ginge/footpedal/STL/pedal assm - switch assm-1 switchbody-1.STL

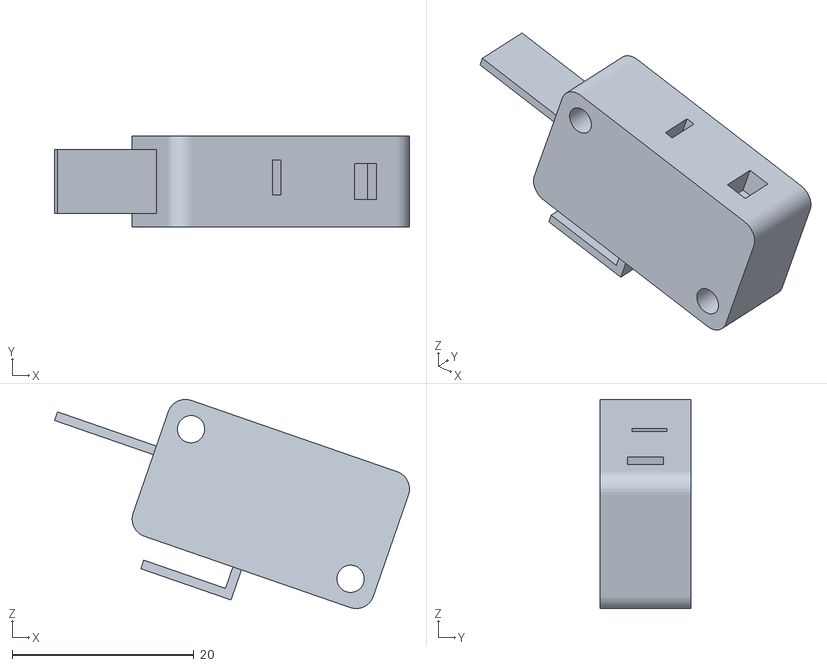
[picture p18: CAD file, 2014-02-17]
STL/pedal assm - switch assm-1 switchbody-1.STL
39.0 x 9.95 x 23.0
