ginge/footpedal/Foot Pedal Sld/pot cog.SLDPRT

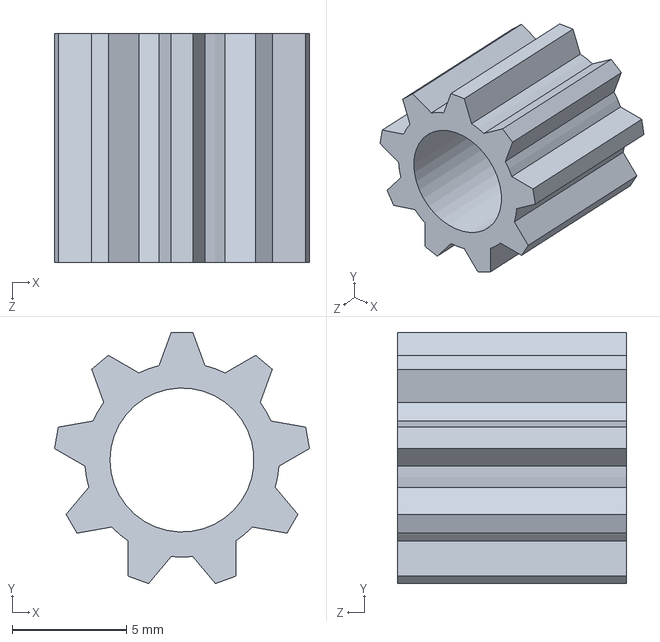
[picture p19: CAD file, 2014-02-17]
Foot Pedal Sld/pot cog.SLDPRT
11.2 x 11.0 x 10.0 mm
