ginge/footpedal/Foot Pedal Sld/pedal.SLDPRT

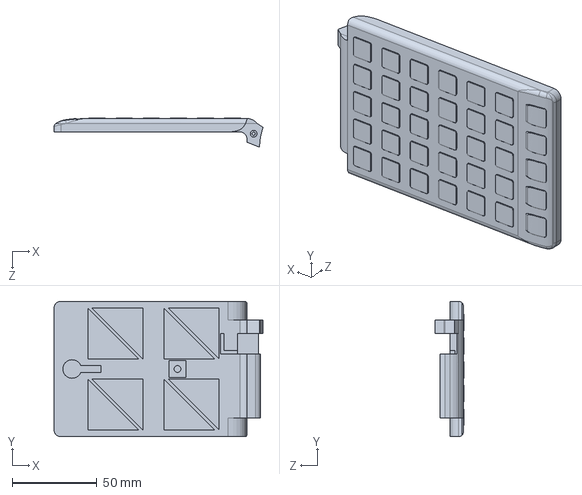
[picture p20: CAD file, 2014-02-17]
Foot Pedal Sld/pedal.SLDPRT
123.5 x 80.0 x 17.4 mm
