ginge/footpedal/STL/pedal assm - pot slide-1.STL

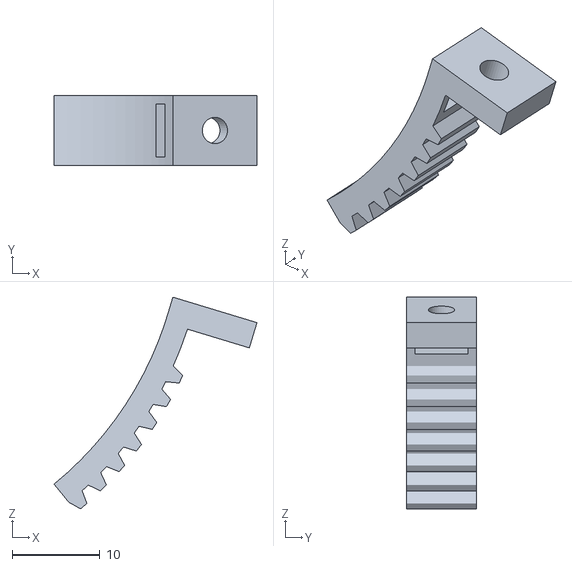
[picture p21: CAD file, 2014-02-17]
STL/pedal assm - pot slide-1.STL
23.1 x 8.00 x 24.1
