ginge/footpedal/Foot Pedal Sld/back panel.SLDPRT

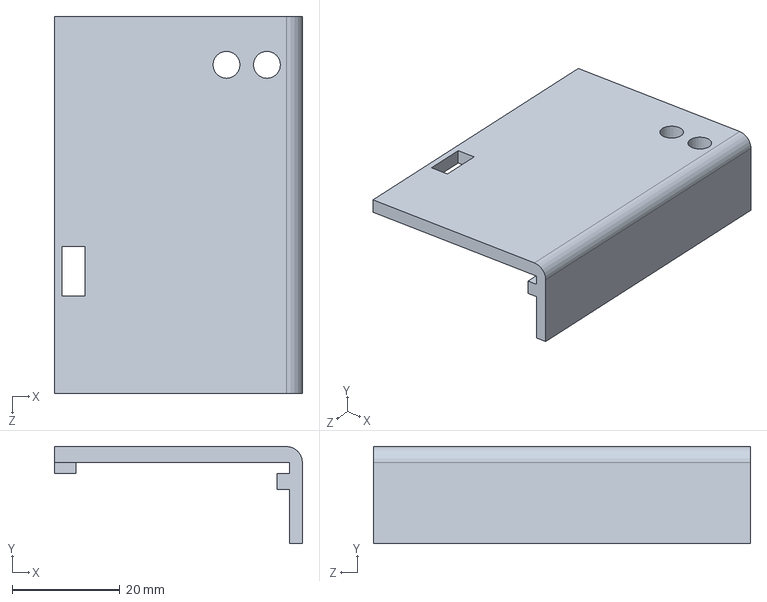
[picture p22: CAD file, 2014-02-17]
Foot Pedal Sld/back panel.SLDPRT
46.0 x 18.0 x 70.0 mm
