ginge/footpedal/STL/pedal assm - peg spring-1.STL

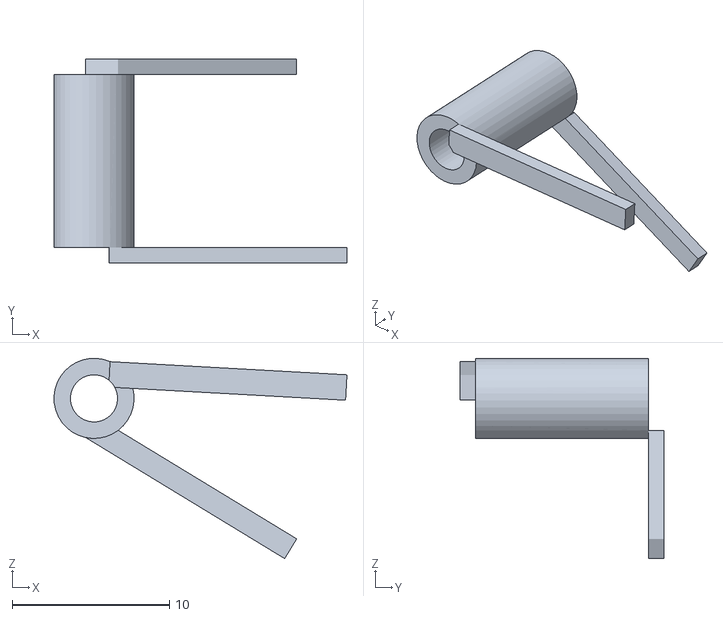
[picture p23: CAD file, 2014-02-17]
STL/pedal assm - peg spring-1.STL
18.6 x 13.0 x 12.7
