ginge/footpedal/Foot Pedal Sld/pot slide.SLDPRT

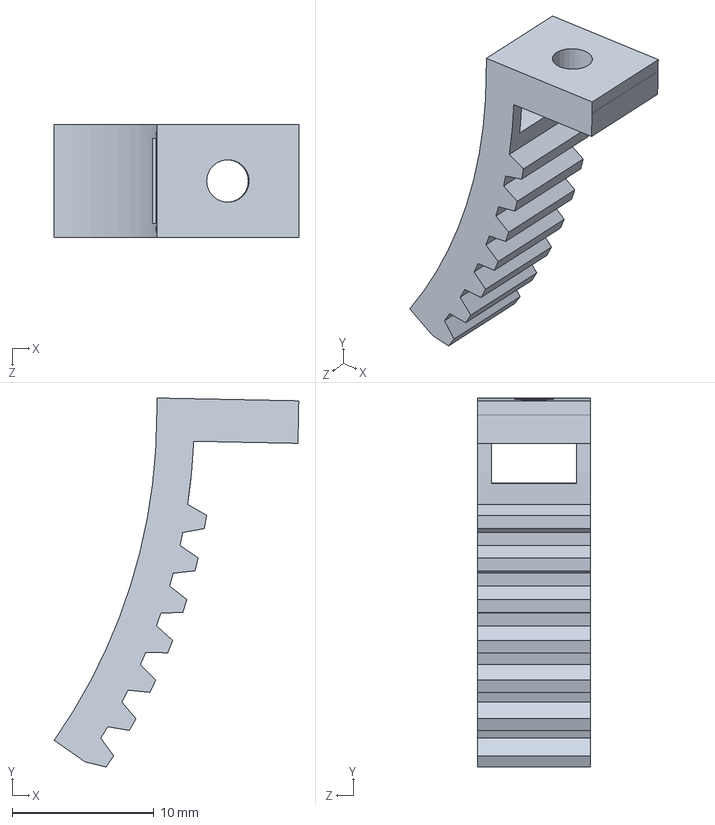
[picture p24: CAD file, 2014-02-17]
Foot Pedal Sld/pot slide.SLDPRT
17.3 x 26.0 x 8.00 mm
