ginge/footpedal/Foot Pedal Sld/spring cap.SLDPRT

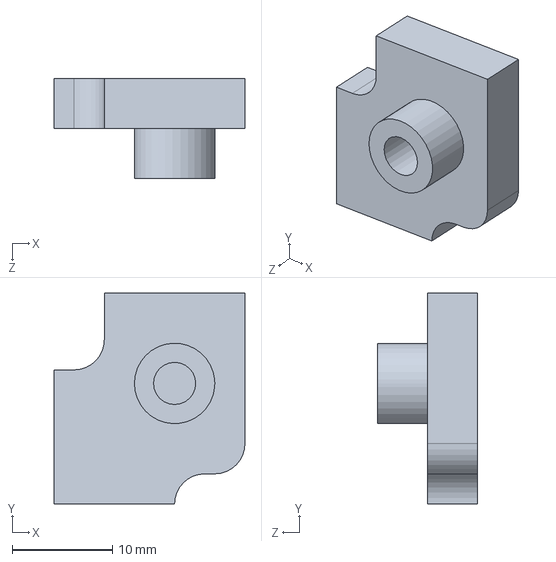
[picture p25: CAD file, 2014-02-17]
Foot Pedal Sld/spring cap.SLDPRT
19.0 x 21.0 x 10.0 mm
