ginge/footpedal/STL/pedal assm - pedal-1.STL

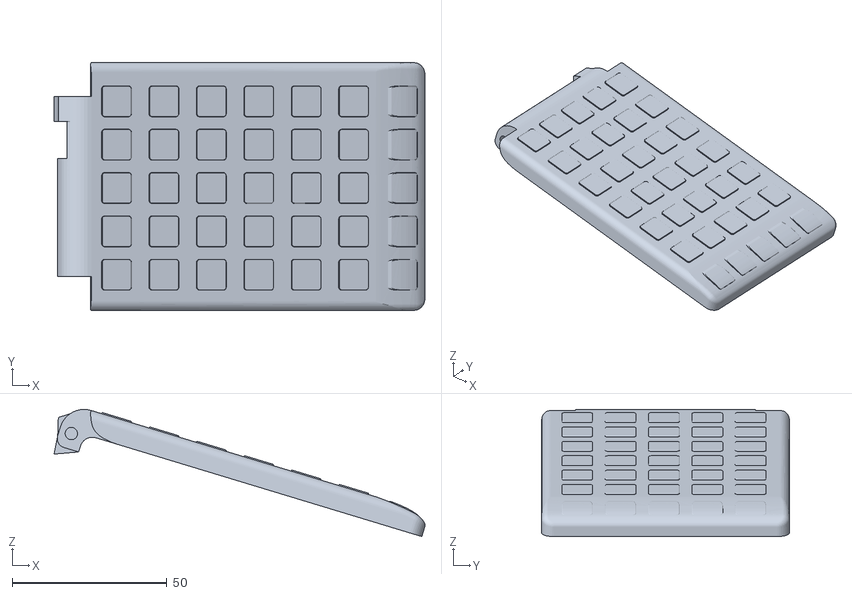
[picture p26: CAD file, 2014-02-17]
STL/pedal assm - pedal-1.STL
119.8 x 80.0 x 41.1
