ginge/footpedal/Foot Pedal Sld/peg spring.SLDPRT

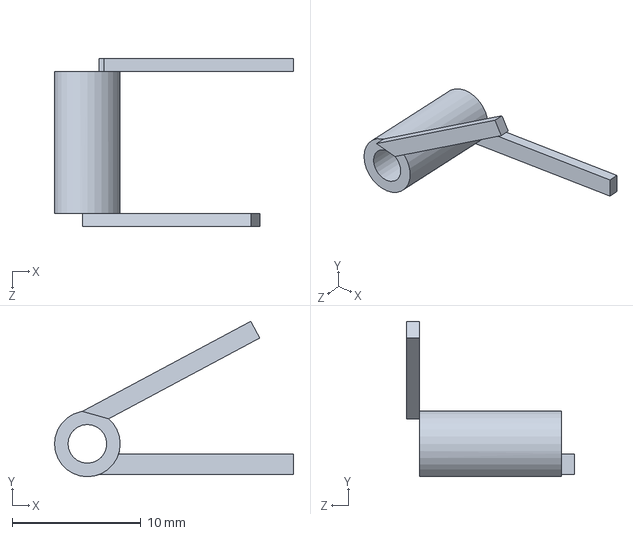
[picture p27: CAD file, 2014-02-17]
Foot Pedal Sld/peg spring.SLDPRT
18.5 x 12.1 x 13.0 mm
