ginge/footpedal/Foot Pedal Sld/front panel.SLDPRT

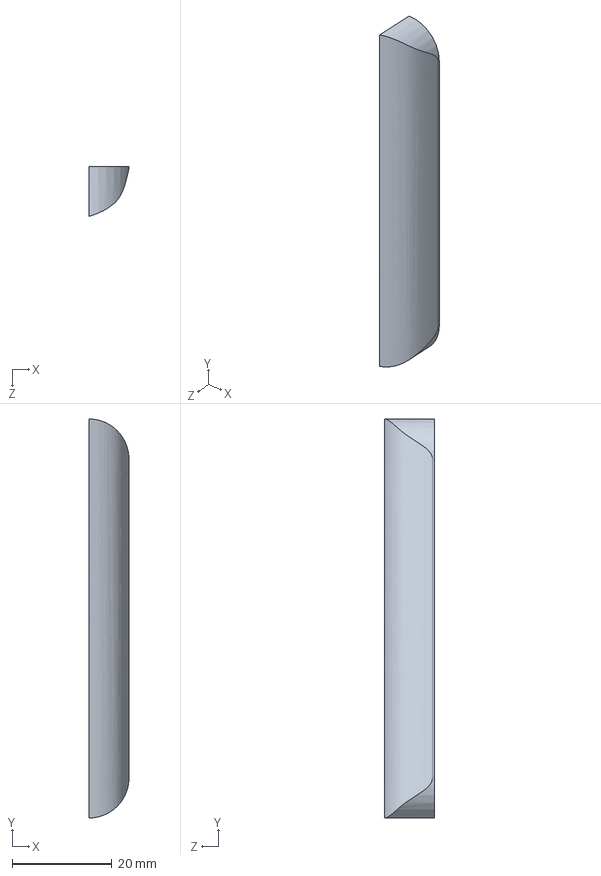
[picture p28: CAD file, 2014-02-17]
Foot Pedal Sld/front panel.SLDPRT
8.00 x 80.0 x 10.0 mm
