ginge/footpedal/STL/pedal assm - teensy3.1-1.STL

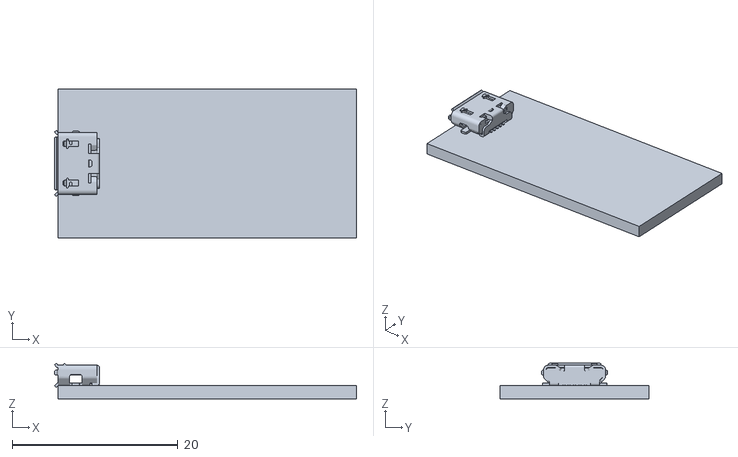
[picture p29: CAD file, 2014-02-17]
STL/pedal assm - teensy3.1-1.STL
36.4 x 18.0 x 4.30
