ginge/footpedal/STL/pedal assm - switch assm-1 button-1.STL

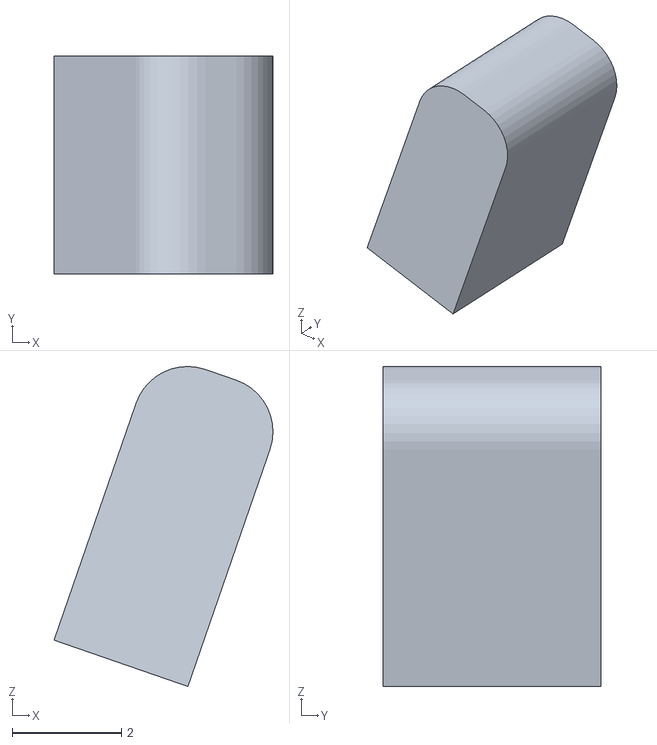
[picture p30: CAD file, 2014-02-17]
STL/pedal assm - switch assm-1 button-1.STL
4.02 x 4.00 x 5.87
